lancer73/ESPHome-Alarm-Clock/images/alarm_clock_light.jpeg

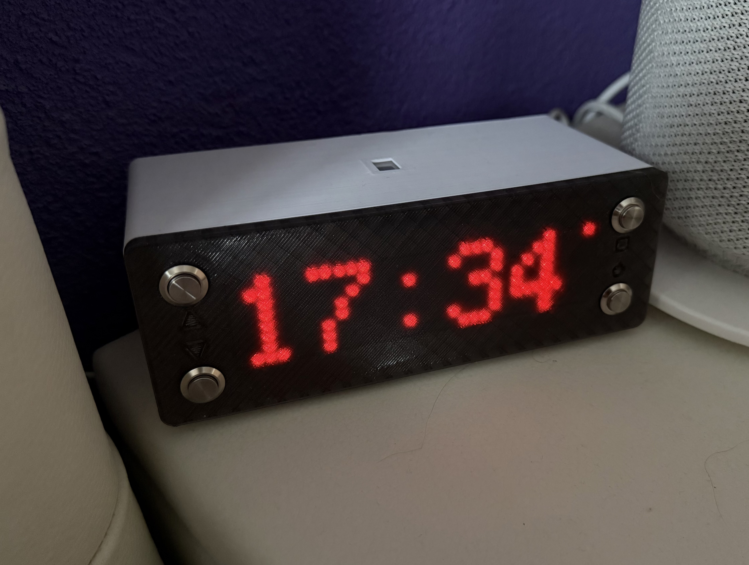
images/alarm_clock_light.jpeg
