lancer73/ESPHome-Alarm-Clock/images/alarm_clock_upsidedown.jpeg

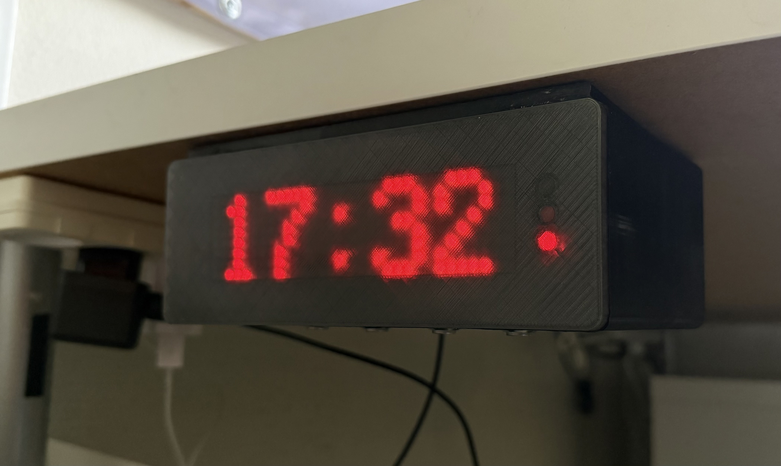
images/alarm_clock_upsidedown.jpeg
